SasaKaranovic/USB-Power-supply-Active-Load-Tester/Hardware/PAL Tester Schematic v0.6 - No connection-hunting.png

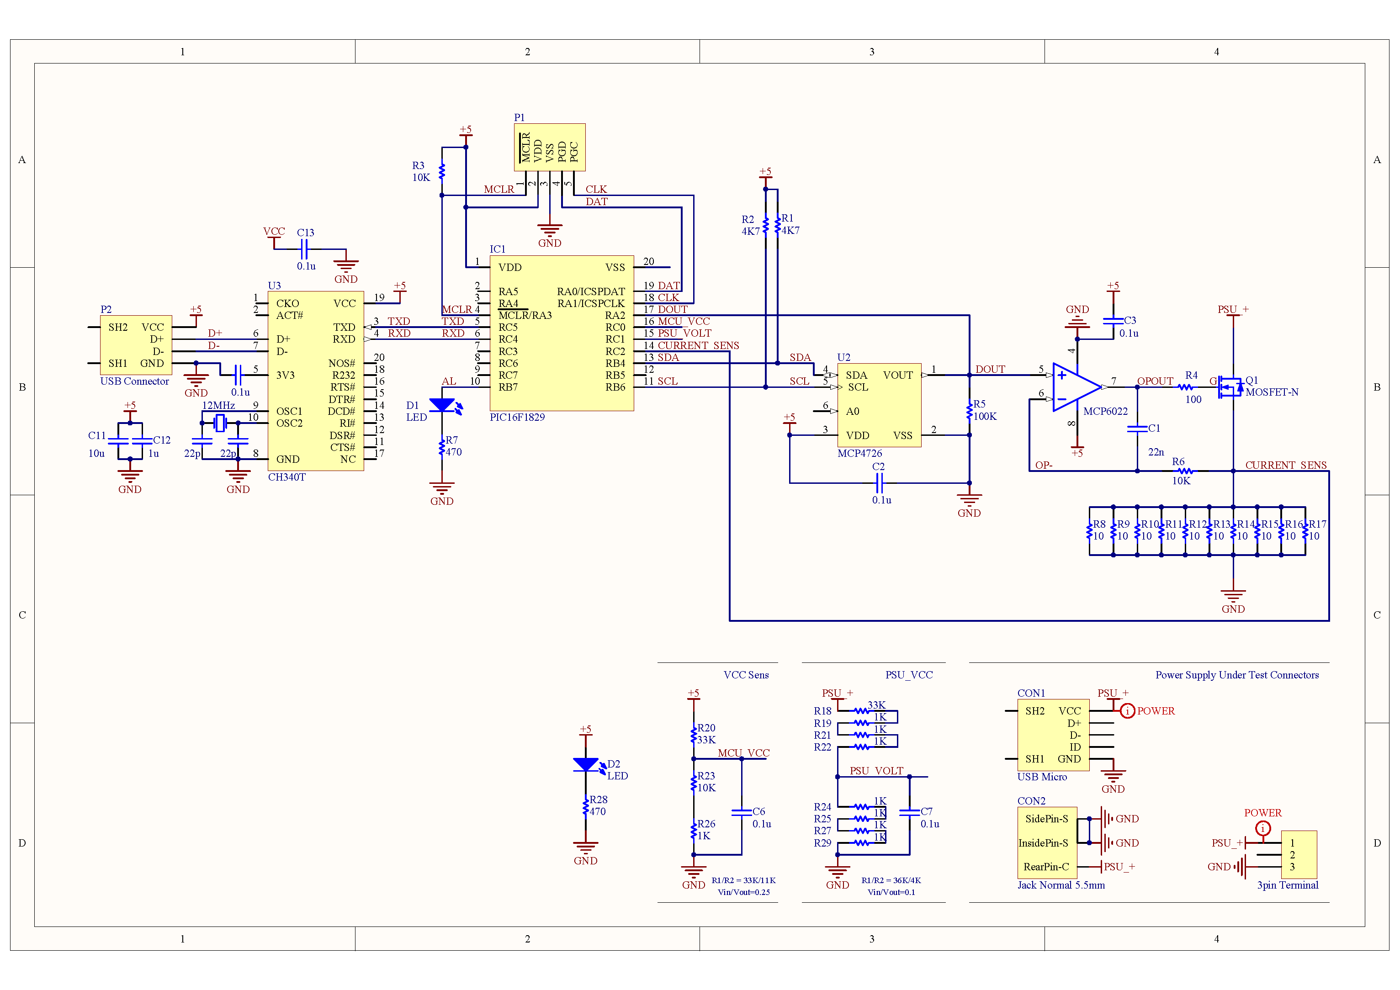
Hardware/PAL Tester Schematic v0.6 - No connection-hunting.png
